siliconchronicles/clock-module/schematic/clock/clock.kicad_sch

## KiCad design schematic/clock/clock.kicad_sch (2024-05-06)

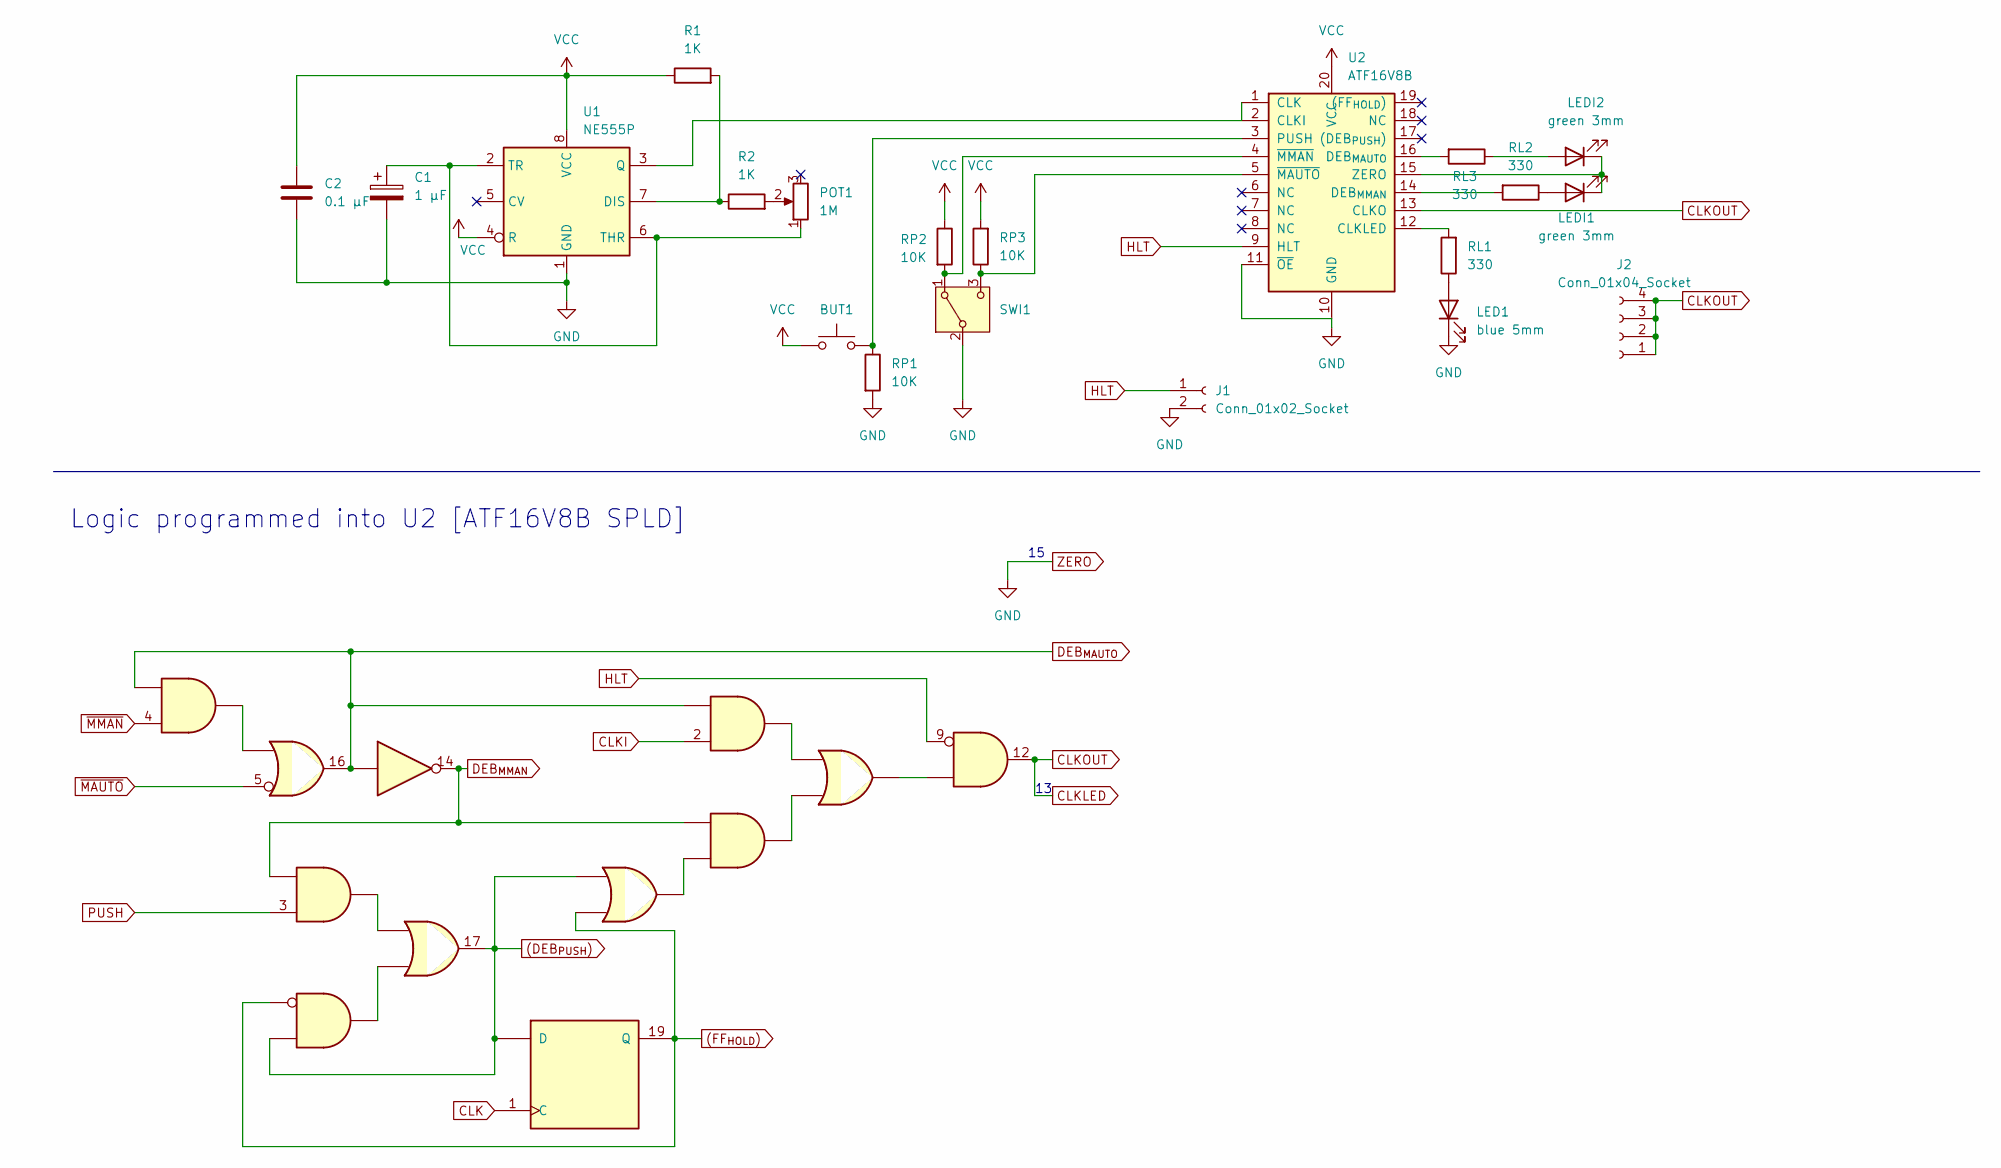
[picture p6: schematic clock.kicad_sch]

Parts:
BUT1: SW_Push
C1: 1 µF
C2: 0.1 µF
J1: Conn_01x02_Socket; PinSocket_1x02_P2.54mm_Vertical
J2: Conn_01x04_Socket; PinSocket_1x04_P2.54mm_Vertical
LED1: blue 5mm; LED_D5.0mm
LEDI1, LEDI2: green 3mm; LED_D3.0mm
POT1: 1M; PinSocket_1x02_P2.54mm_Vertical
R1: 1K; R_Axial_DIN0207_L6.3mm_D2.5mm_P2.54mm_Vertical
R2: 1K; R_Axial_DIN0207_L6.3mm_D2.5mm_P5.08mm_Vertical
RL1, RL2, RL3: 330; R_Axial_DIN0207_L6.3mm_D2.5mm_P5.08mm_Vertical
RP1: 10K; R_Axial_DIN0207_L6.3mm_D2.5mm_P7.62mm_Horizontal
RP2: 10K; R_Axial_DIN0207_L6.3mm_D2.5mm_P10.16mm_Horizontal
RP3: 10K; R_Axial_DIN0207_L6.3mm_D2.5mm_P2.54mm_Vertical
SWI1: SW_SPDT
U1: NE555P; DIP-8_W7.62mm
U2: ATF16V8B; CERDIP-20_W7.62mm_SideBrazed_Socket
U2:2, U2:9, U2:16, U2:17, U2:19, U2:x0, U2:x2, U2:x4, U2:x5, U3: (no value)
U2:04, U2:14: ATF16V8

Connections:
(DEB_{PUSH}): U2:17.17, U2:19. (D), U2:x0., U2:x4.
(FF_{HOLD}): U2:19.19 (Q), U2:x0., U2:x4.
CLK: U2:19.1 (C)
CLKI: U2:2.2
CLKLED: J2.1, J2.2, J2.3, J2.4, U2.13 (CLKO), U2:9.12
DEB_{MAUTO}: U2:2., U2:04., U2:14., U2:16.16
DEB_{MMAN}: U2:14.14, U2:x5., U3.
GND: C1.2, C2.2, J1.2, LED1.1 (K), RP1.2, SWI1.2 (B), U1.1 (GND), U2.10 (GND), U2.11 (~OE)
HLT: J1.1, U2.9 (HLT), U2:9.9
unnamed: BUT1.2, RP1.1, U2.3 (PUSH)
unnamed: C1.1, POT1.1, U1.2 (TR), U1.6 (THR)
unnamed: LED1.2 (A), RL1.1
unnamed: LEDI1.1 (K), LEDI2.1 (K), U2.15 (ZERO)
unnamed: LEDI1.2 (A), RL2.1
unnamed: LEDI2.2 (A), RL3.1
unnamed: POT1.2, R2.2
unnamed: R1.2, R2.1, U1.7 (DIS)
unnamed: RL1.2, U2.12 (CLKLED)
unnamed: RL2.2, U2.14 (DEB_{MMAN})
unnamed: RL3.2, U2.16 (DEB_{MAUTO})
unnamed: RP2.2, SWI1.1 (A), U2.4 (~MMAN)
unnamed: RP3.1, SWI1.3 (C), U2.5 (~MAUTO)
unnamed: U1.3 (Q), U2.1 (CLK), U2.2 (CLKI)
unnamed: U2:2., U2:x2.
unnamed: U2:04., U2:16.
unnamed: U2:9., U2:x2.
unnamed: U2:17., U2:x0., U3.
unnamed: U2:x2., U2:x5.
unnamed: U2:x4., U2:x5.
PUSH: U3.3
VCC: BUT1.1, C2.1, R1.1, RP2.1, RP3.2, U1.4 (R), U1.8 (VCC), U2.20 (VCC)
~MAUTO: U2:16.5
~MMAN: U2:04.4

Notes on the sheet:
Logic programmed into U2 [ATF16V8B SPLD]
